wntrblm/Micronova/user_guide/docs/images/1-kit-contents-1.jpg

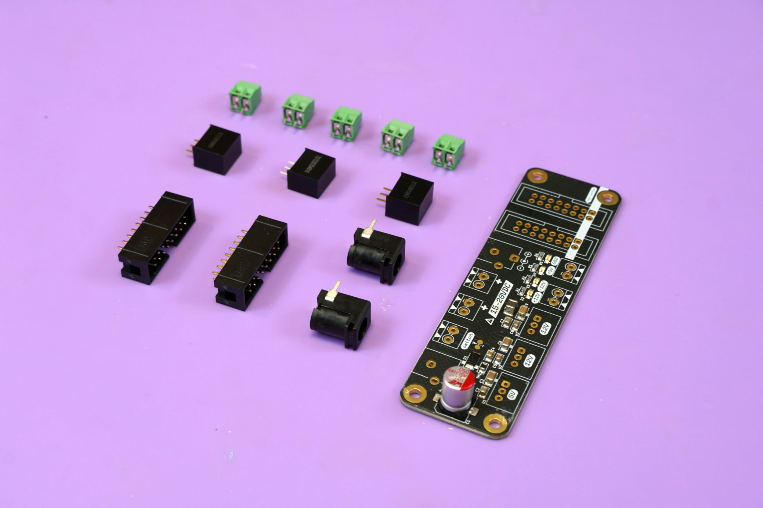
user_guide/docs/images/1-kit-contents-1.jpg
