wntrblm/Micronova/user_guide/docs/images/9-all-terminals-soldered-back.jpg

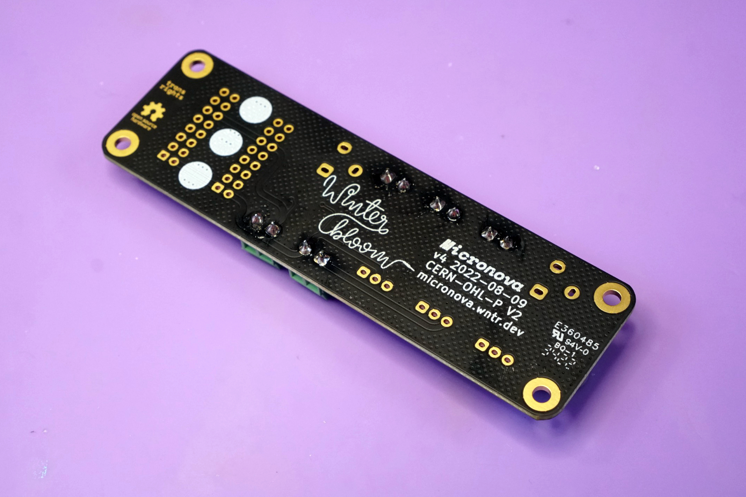
user_guide/docs/images/9-all-terminals-soldered-back.jpg
