wntrblm/Micronova/user_guide/docs/images/29-complete.jpg

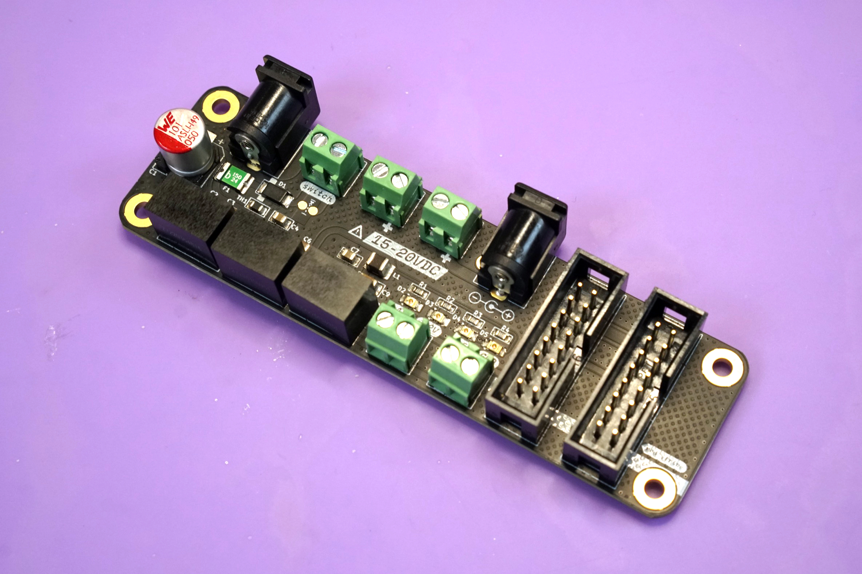
user_guide/docs/images/29-complete.jpg
